Inclusive-Bytes/CrowdClock/src/EffectOrbit.cpp

#include "EffectOrbit.h"

#include <FastLED.h>

static const uint8_t orbitPattern[] = {
    1,1,0,0,0,0,0,1,1,1,0,0,0,0,0,1,
    1,1,1,0,0,0,0,0,1,1,1,0,0,0,0,0,
    0,1,1,1,0,0,0,0,0,1,1,1,0,0,0,0,
    0,0,1,1,1,0,0,0,0,0,1,1,1,0,0,0,
    0,0,0,1,1,1,0,0,0,0,0,1,1,1,0,0,
    0,0,0,0,1,1,1,0,0,0,0,0,1,1,1,0,
    0,0,0,0,0,1,1,1,0,0,0,0,0,1,1,1,
    1,0,0,0,0,0,1,1,1,0,0,0,0,0,1,1
};

EffectOrbit::EffectOrbit(CRGB color, int numLeds)
: GenericFlasher(color, numLeds)
{
    m_speedScaler = 8;
    m_numStages = sizeof(orbitPattern) / numLeds;
}

const uint8_t* const EffectOrbit::GetTable()
{
    return orbitPattern;
}
